oskitone/scout_2_prototype/arduino/scout_2_prototype/Frequency.cpp

#include "Frequency.h"
#include "Arduino.h"
#include "Notes.h"

Frequency::Frequency(int glide, int cyclesPerGlideMax) {
  _glide = glide;
  _cyclesPerGlideMax = cyclesPerGlideMax;
}

float Frequency::get() { return _frequency; }

uint16_t Frequency::getHalfPeriod() { return _halfPeriodMicroseconds; }

inline uint16_t castAndRound(float value) { return value + .5f; }

void Frequency::update(float target, int glide) {
  _target = target;
  bool needsUpdate = _frequency != _target;

  if (needsUpdate) {
    if ((_frequency == 0) || (glide == 0)) {
      _frequency = _target;
    } else {
      if (_target != _previousTarget) {
        _glideStep = abs(_target - _previousTarget) /
                     (float(glide) / GLIDE_MAX * _cyclesPerGlideMax);
      }

      _frequency = (_target > _frequency)
                       ? min(_target, _frequency + _glideStep)
                       : max(_target, _frequency - _glideStep);
    }
    _halfPeriodMicroseconds = castAndRound(1000000.0f / _frequency / 2.0f);
  }

  if (!needsUpdate) {
    _previousTarget = _target;
  }
}

void Frequency::reset() {
  _frequency = 0;
  _halfPeriodMicroseconds = 0;
}

void Frequency::print() {
  Serial.println("frequency:" + String(_frequency) +
                 ",halfPeriodMicroseconds:" + String(_halfPeriodMicroseconds) +
                 ",target:" + String(_target) +
                 ",previousTargetFrequency:" + String(_previousTarget));
}
